kingyoPiyo/RasPico_SHIBAKI_Board/firmware/udp_test/udp.c

#include "udp.h"
#include "pico/stdlib.h"

#if UDP_DMA_EN
#include "hardware/dma.h"
#endif

// 4B5B convert table
const static uint16_t __not_in_flash("tbl_4b5b") tbl_4b5b[256] = {
    0b1111011110, 0b1111001001, 0b1111010100, 0b1111010101, 0b1111001010, 0b1111001011, 0b1111001110, 0b1111001111, 0b1111010010, 0b1111010011, 0b1111010110, 0b1111010111, 0b1111011010, 0b1111011011, 0b1111011100, 0b1111011101,
    0b0100111110, 0b0100101001, 0b0100110100, 0b0100110101, 0b0100101010, 0b0100101011, 0b0100101110, 0b0100101111, 0b0100110010, 0b0100110011, 0b0100110110, 0b0100110111, 0b0100111010, 0b0100111011, 0b0100111100, 0b0100111101,
    0b1010011110, 0b1010001001, 0b1010010100, 0b1010010101, 0b1010001010, 0b1010001011, 0b1010001110, 0b1010001111, 0b1010010010, 0b1010010011, 0b1010010110, 0b1010010111, 0b1010011010, 0b1010011011, 0b1010011100, 0b1010011101,
    0b1010111110, 0b1010101001, 0b1010110100, 0b1010110101, 0b1010101010, 0b1010101011, 0b1010101110, 0b1010101111, 0b1010110010, 0b1010110011, 0b1010110110, 0b1010110111, 0b1010111010, 0b1010111011, 0b1010111100, 0b1010111101,
    0b0101011110, 0b0101001001, 0b0101010100, 0b0101010101, 0b0101001010, 0b0101001011, 0b0101001110, 0b0101001111, 0b0101010010, 0b0101010011, 0b0101010110, 0b0101010111, 0b0101011010, 0b0101011011, 0b0101011100, 0b0101011101,
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
    dma_conf = dma_channel_get_default_config(dma_ch);
    channel_config_set_transfer_data_size(&dma_conf, DMA_SIZE_8);
#else
    _make_crc_table();
#endif
}


void __time_critical_func(udp_packet_gen)(uint32_t *buf, uint8_t *udp_payload) {
    uint16_t udp_chksum = 0;
    uint32_t i, idx = 0;

    // Calculate the ip check sum
    ip_chk_sum1 = 0x0000C512 + ip_identifier + ip_total_len + (DEF_IP_ADR_SRC1 << 8) + DEF_IP_ADR_SRC2 + (DEF_IP_ADR_SRC3 << 8) + DEF_IP_ADR_SRC4 +
                  (DEF_IP_DST_DST1 << 8) + DEF_IP_DST_DST2 + (DEF_IP_DST_DST3 << 8) + DEF_IP_DST_DST4;
    ip_chk_sum2 = (ip_chk_sum1 & 0x0000FFFF) + (ip_chk_sum1 >> 16);
    ip_chk_sum3 = ~((ip_chk_sum2 & 0x0000FFFF) + (ip_chk_sum2 >> 16));

    //==========================================================================
    ip_identifier++;

    // Preamble
    for (i = 0; i < 7; i++) {
        data_8b[idx++] = 0x55;
    }
    // SFD
    data_8b[idx++] = 0xD5;
    // Destination MAC Address
    data_8b[idx++] = (DEF_ETH_DST_MAC >> 40) & 0xFF;
    data_8b[idx++] = (DEF_ETH_DST_MAC >> 32) & 0xFF;
    data_8b[idx++] = (DEF_ETH_DST_MAC >> 24) & 0xFF;
    data_8b[idx++] = (DEF_ETH_DST_MAC >> 16) & 0xFF;
    data_8b[idx++] = (DEF_ETH_DST_MAC >>  8) & 0xFF;
    data_8b[idx++] = (DEF_ETH_DST_MAC >>  0) & 0xFF;
    // Source MAC Address
    data_8b[idx++] = (DEF_ETH_SRC_MAC >> 40) & 0xFF;
    data_8b[idx++] = (DEF_ETH_SRC_MAC >> 32) & 0xFF;
    data_8b[idx++] = (DEF_ETH_SRC_MAC >> 24) & 0xFF;
    data_8b[idx++] = (DEF_ETH_SRC_MAC >> 16) & 0xFF;
    data_8b[idx++] = (DEF_ETH_SRC_MAC >>  8) & 0xFF;
    data_8b[idx++] = (DEF_ETH_SRC_MAC >>  0) & 0xFF;
    // Ethernet Type
    data_8b[idx++] = (eth_type >>  8) & 0xFF;
    data_8b[idx++] = (eth_type >>  0) & 0xFF;
    // IP Header
    data_8b[idx++] = (ip_version << 4) | (ip_head_len & 0x0F);
    data_8b[idx++] = (ip_type_of_service >>  0) & 0xFF;
    data_8b[idx++] = (ip_total_len >>  8) & 0xFF;
    data_8b[idx++] = (ip_total_len >>  0) & 0xFF;
    data_8b[idx++] = (ip_identifier >>  8) & 0xFF;
    data_8b[idx++] = (ip_identifier >>  0) & 0xFF;
    data_8b[idx++] = 0x00;
    data_8b[idx++] = 0x00;
    data_8b[idx++] = 0x80;
    data_8b[idx++] = 0x11;
    // IP Check SUM
    data_8b[idx++] = (ip_chk_sum3 >>  8) & 0xFF;
    data_8b[idx++] = (ip_chk_sum3 >>  0) & 0xFF;
    // IP Source
    data_8b[idx++] = DEF_IP_ADR_SRC1;
    data_8b[idx++] = DEF_IP_ADR_SRC2;
    data_8b[idx++] = DEF_IP_ADR_SRC3;
    data_8b[idx++] = DEF_IP_ADR_SRC4;
    // IP Destination
    data_8b[idx++] = DEF_IP_DST_DST1;
    data_8b[idx++] = DEF_IP_DST_DST2;
    data_8b[idx++] = DEF_IP_DST_DST3;
    data_8b[idx++] = DEF_IP_DST_DST4;
    // UDP header
    data_8b[idx++] = (DEF_UDP_SRC_PORTNUM >>  8) & 0xFF;
    data_8b[idx++] = (DEF_UDP_SRC_PORTNUM >>  0) & 0xFF;
    data_8b[idx++] = (DEF_UDP_DST_PORTNUM >>  8) & 0xFF;
    data_8b[idx++] = (DEF_UDP_DST_PORTNUM >>  0) & 0xFF;
    data_8b[idx++] = (DEF_UDP_LEN >>  8) & 0xFF;
    data_8b[idx++] = (DEF_UDP_LEN >>  0) & 0xFF;
    data_8b[idx++] = (udp_chksum >>  8) & 0xFF;
    data_8b[idx++] = (udp_chksum >>  0) & 0xFF;
    
    // UDP payload
#if UDP_DMA_EN
    // Copy using DMA transfer
    channel_config_set_read_increment(&dma_conf, true);
    channel_config_set_write_increment(&dma_conf, true);
    dma_channel_configure (
        dma_ch ,                // Channel to be configured
        &dma_conf,              // The configuration we just created
        &data_8b[idx],          // Destination address
        udp_payload,            // Source address
        DEF_UDP_PAYLOAD_SIZE,   // Number of transfers
        true                    // Start yet
    );
    idx += DEF_UDP_PAYLOAD_SIZE;
    dma_channel_wait_for_finish_blocking(dma_ch);  // Wait for transfer
#else
    for (i = 0; i < DEF_UDP_PAYLOAD_SIZE; i++) {
        data_8b[idx++] = udp_payload[i];
    }
#endif

    //==========================================================================
    // FCS Calc
    //==========================================================================
#if UDP_DMA_EN
    channel_config_set_read_increment(&dma_conf, true);
    channel_config_set_write_increment(&dma_conf, false);
    dma_channel_configure (
        dma_ch,                 // Channel to be configured
        &dma_conf,              // The configuration we just created
        NULL,                   // Destination address
        &data_8b[8],            // Source address
        (idx-8),                // Number of transfers
        false                   // Don't start yet
    );
    dma_sniffer_enable(dma_ch, 1, true);                    // CRC Mode = Calculate a CRC-32 (IEEE802.3 polynomial) with bit reversed data
    hw_set_bits(&dma_hw->sniff_ctrl,
               (DMA_SNIFF_CTRL_OUT_INV_BITS | DMA_SNIFF_CTRL_OUT_REV_BITS));
    dma_hw->sniff_data = 0xffffffff;                        // Initialize CRC-32 seed value
    dma_channel_set_read_addr(dma_ch, &data_8b[8], true);   // Start transfer
    dma_channel_wait_for_finish_blocking(dma_ch);           // Wait for transfer
    uint32_t crc = dma_hw->sniff_data;
#else
    uint32_t crc = 0xffffffff;
    for (i = 8; i < idx; i++) {
        crc = (crc >> 8) ^ crc_table[(crc ^ data_8b[i]) & 0xFF];
    }
    crc ^= 0xffffffff;
#endif

    data_8b[idx++] = (crc >>  0) & 0xFF;
    data_8b[idx++] = (crc >>  8) & 0xFF;
    data_8b[idx++] = (crc >> 16) & 0xFF;
    data_8b[idx++] = (crc >> 24) & 0xFF;

    //==========================================================================
    // Encording 4b5b & NRZI Encoder
    //==========================================================================
    uint16_t ob;
    uint32_t ans;

    // Sync, Start delimiter [9:5]=K, [4:0]=J
    ans = tbl_nrzi[0b1000111000];
    buf[0] = ans;
    ob = (ans << 1) & 0x400;
    
    for (i = 1; i < DEF_UDP_BUF_SIZE; i++) {
        ans = tbl_nrzi[ob + tbl_4b5b[data_8b[i]]];
        ob = (ans << 1) & 0x400;
        buf[i] = ans;
    }

    // End delimiter [9:5]=R, [4:0]=T
    buf[DEF_UDP_BUF_SIZE] = tbl_nrzi[ob + 0b0011101101];
}
