kingyoPiyo/RasPico_SHIBAKI_Board/firmware/hwtest/tbl_8b10b.c

#include "tbl_8b10b.h"

static bool disp_enc = false;

static const uint16_t enc_tbl[512] = {
    // RD-
    0b1001110100, 0b0111010100, 0b1011010100, 0b1100011011, 0b1101010100, 0b1010011011, 0b0110011011, 0b1110001011,
    0b1110010100, 0b1001011011, 0b0101011011, 0b1101001011, 0b0011011011, 0b1011001011, 0b0111001011, 0b0101110100,
    0b0110110100, 0b1000111011, 0b0100111011, 0b1100101011, 0b0010111011, 0b1010101011, 0b0110101011, 0b1110100100,
    0b1100110100, 0b1001101011, 0b0101101011, 0b1101100100, 0b0011101011, 0b1011100100, 0b0111100100, 0b1010110100,
    0b1001111001, 0b0111011001, 0b1011011001, 0b1100011001, 0b1101011001, 0b1010011001, 0b0110011001, 0b1110001001,
    0b1110011001, 0b1001011001, 0b0101011001, 0b1101001001, 0b0011011001, 0b1011001001, 0b0111001001, 0b0101111001,
    0b0110111001, 0b1000111001, 0b0100111001, 0b1100101001, 0b0010111001, 0b1010101001, 0b0110101001, 0b1110101001,
    0b1100111001, 0b1001101001, 0b0101101001, 0b1101101001, 0b0011101001, 0b1011101001, 0b0111101001, 0b1010111001,
    0b1001110101, 0b0111010101, 0b1011010101, 0b1100010101, 0b1101010101, 0b1010010101, 0b0110010101, 0b1110000101,
    0b1110010101, 0b1001010101, 0b0101010101, 0b1101000101, 0b0011010101, 0b1011000101, 0b0111000101, 0b0101110101,
    0b0110110101, 0b1000110101, 0b0100110101, 0b1100100101, 0b0010110101, 0b1010100101, 0b0110100101, 0b1110100101,
    0b1100110101, 0b1001100101, 0b0101100101, 0b1101100101, 0b0011100101, 0b1011100101, 0b0111100101, 0b1010110101,
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
{
    uint32_t ret = 0;

    if (ken) {
        // K28.5
        if (disp_enc) {
            ret = 0b1100000101;
        } else {
            ret = 0b0011111010;
        }
    } else {
        ret = enc_tbl[data + (disp_enc ? 256 : 0)];
    }
    disp_enc = !disp_enc;

    return ret;
}
